kyovchev/educational-robot/STLs/Body-Spacer.stl

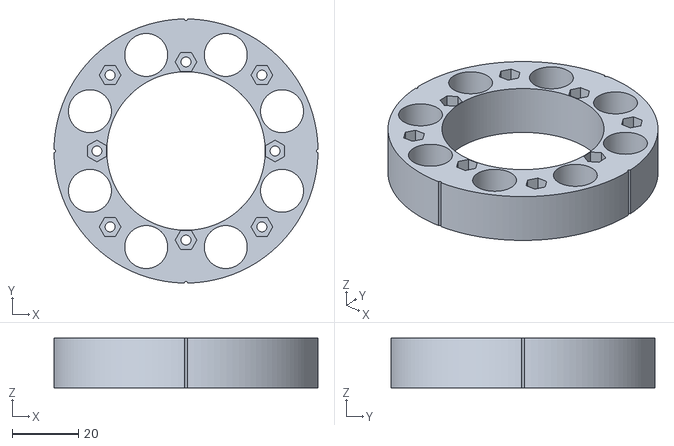
[picture p15: CAD file, 2026-03-13]
STLs/Body-Spacer.stl
80.0 x 80.0 x 15.0
