kyovchev/educational-robot/STLs/Body-90degreeCover.stl

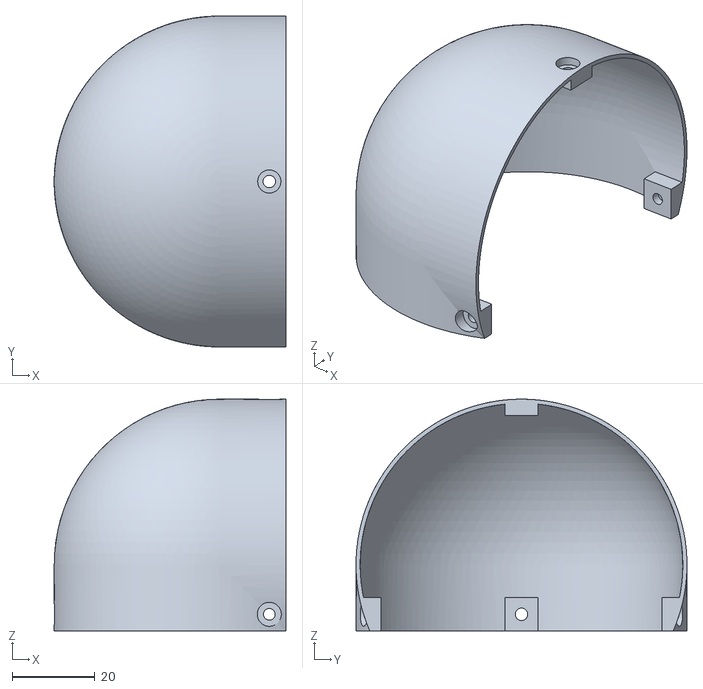
[picture p16: CAD file, 2026-03-13]
STLs/Body-90degreeCover.stl
56.0 x 80.0 x 56.0
