kyovchev/educational-robot/STLs/Base-Bracket.stl

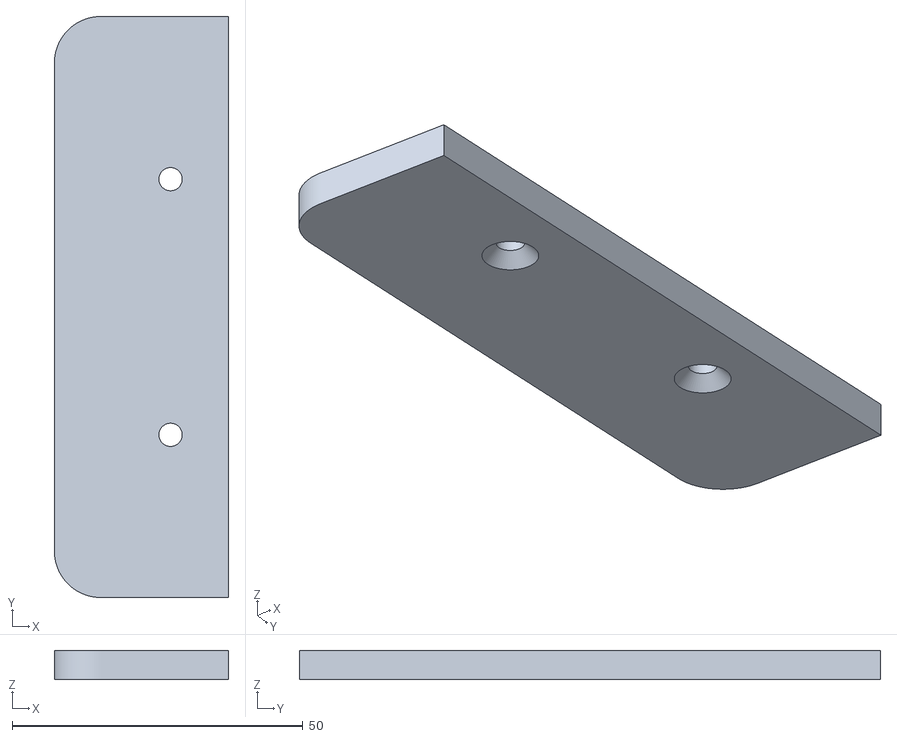
[picture p17: CAD file, 2026-03-13]
STLs/Base-Bracket.stl
30.0 x 100.0 x 5.00
